Aboyd656/RetroPie-Switch/check.png

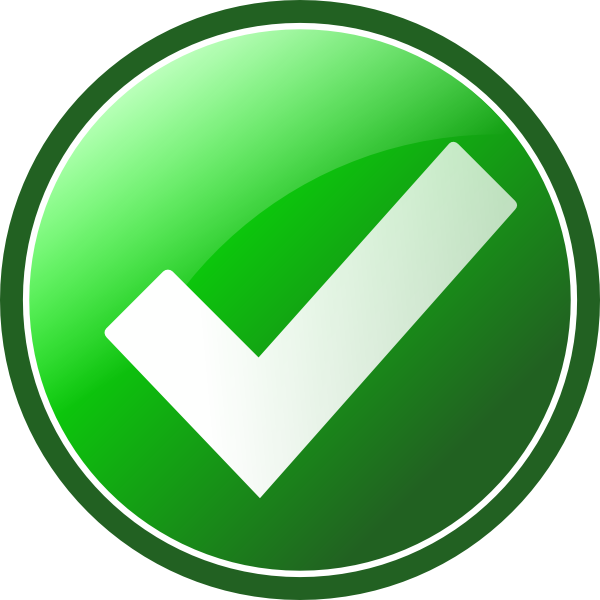
check.png
