Aboyd656/RetroPie-Switch/Debian.jpg

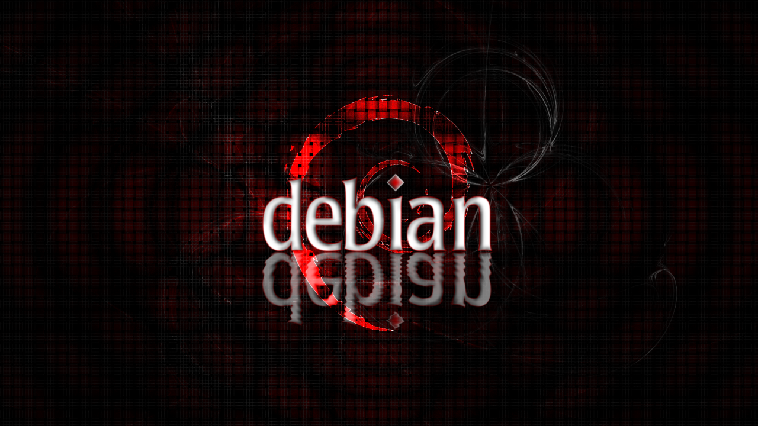
Debian.jpg
